Pauliomono/Kevin-the-Robot-Dog/CAD Files/servo motor/1.JPG

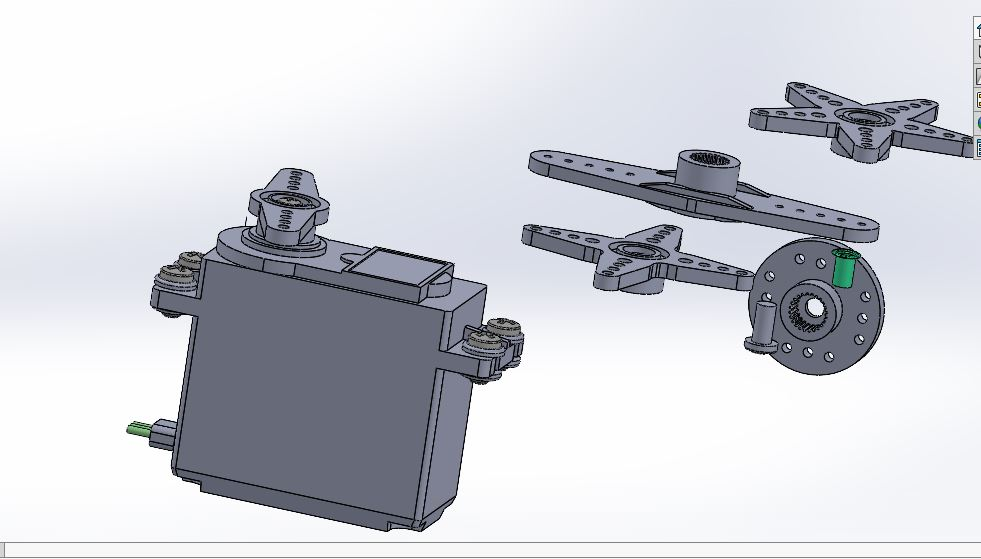
CAD Files/servo motor/1.JPG
