Pauliomono/Kevin-the-Robot-Dog/CAD Files/servo motor/2.JPG

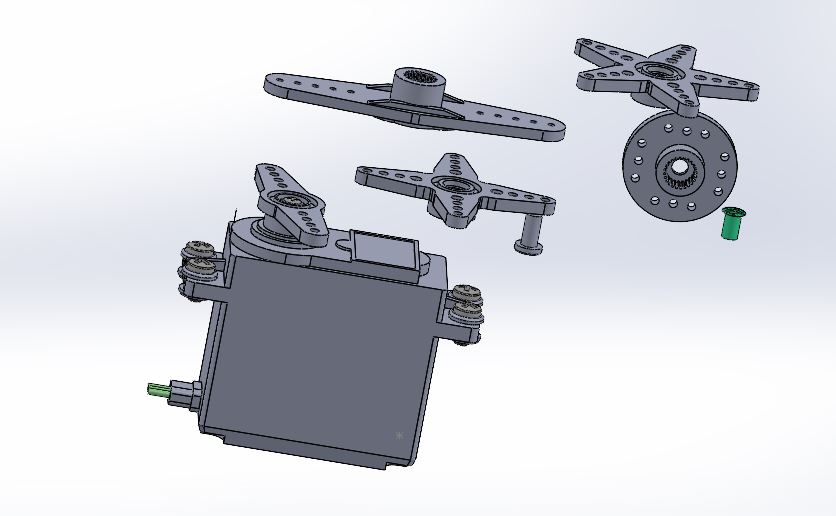
CAD Files/servo motor/2.JPG
