Pauliomono/Kevin-the-Robot-Dog/CAD Files/servo motor/3.JPG

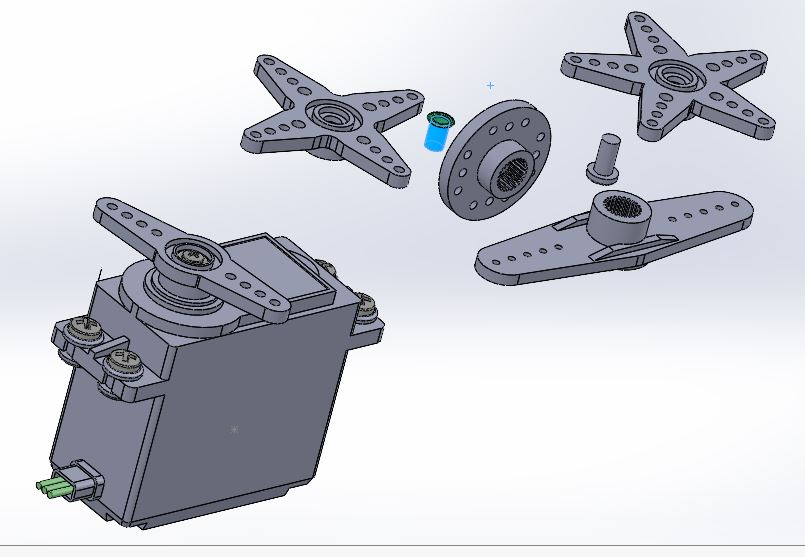
CAD Files/servo motor/3.JPG
