Pauliomono/Kevin-the-Robot-Dog/CAD Files/servo motor/4.JPG

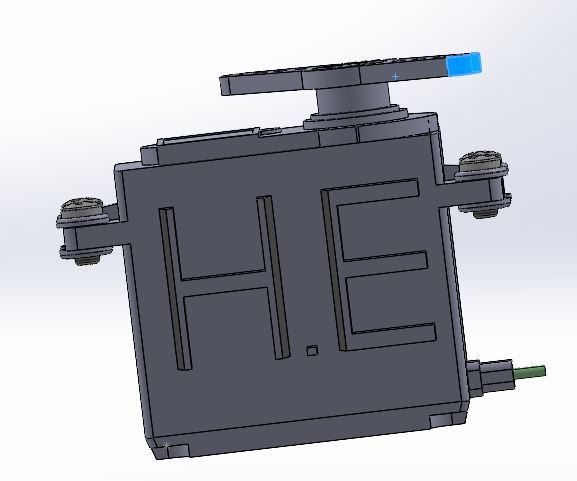
CAD Files/servo motor/4.JPG
