Pauliomono/Kevin-the-Robot-Dog/CAD Files/servo motor/part7.SLDPRT

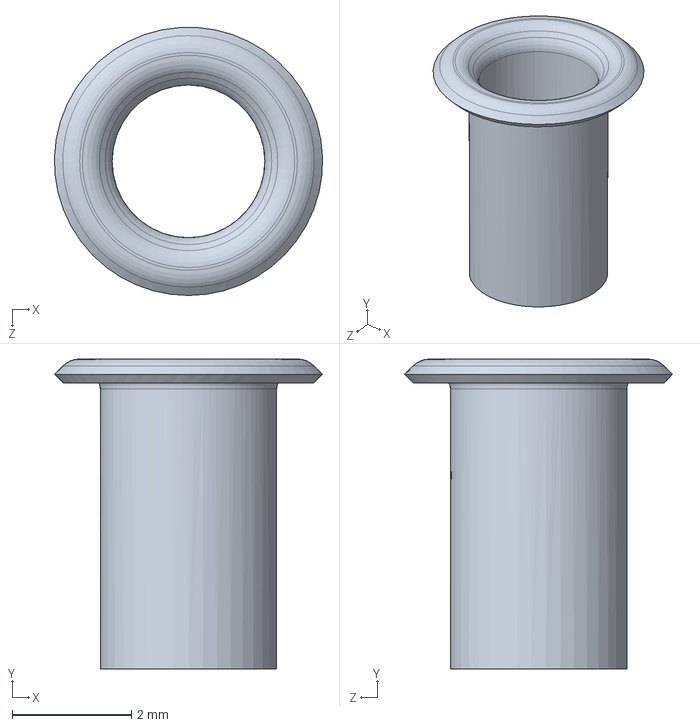
[picture p26: CAD file, 2022-06-29]
CAD Files/servo motor/part7.SLDPRT
4.50 x 5.20 x 4.49 mm
