Pauliomono/Kevin-the-Robot-Dog/CAD Files/servo motor/Parça2 - Kopya.SLDPRT

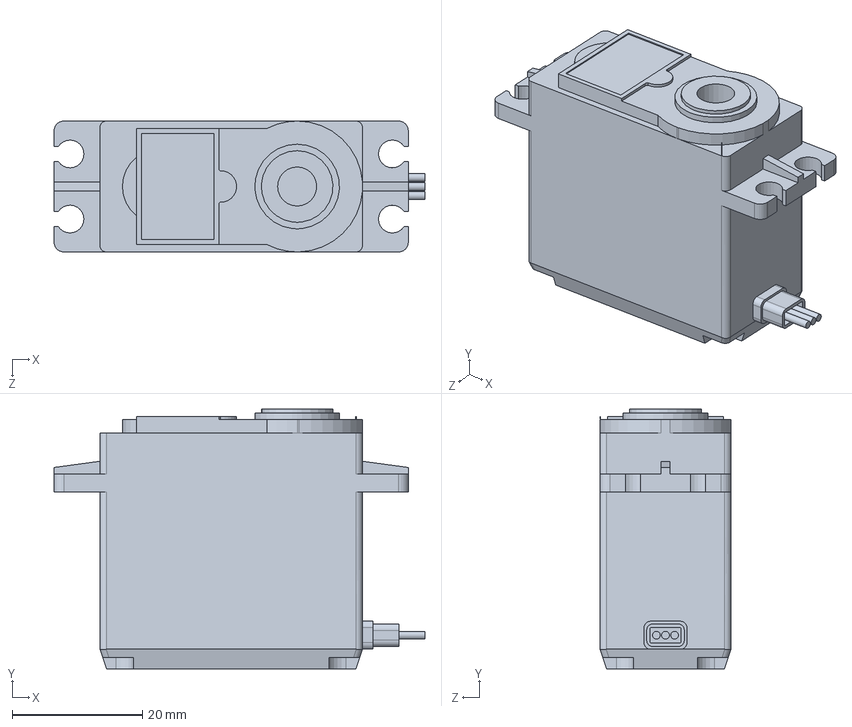
[picture p27: CAD file, 2022-06-29]
CAD Files/servo motor/Parça2 - Kopya.SLDPRT
57.0 x 39.8 x 20.1 mm
