Pauliomono/Kevin-the-Robot-Dog/CAD Files/servo-brackets-2.snapshot.3/U Long Bracket.SLDPRT

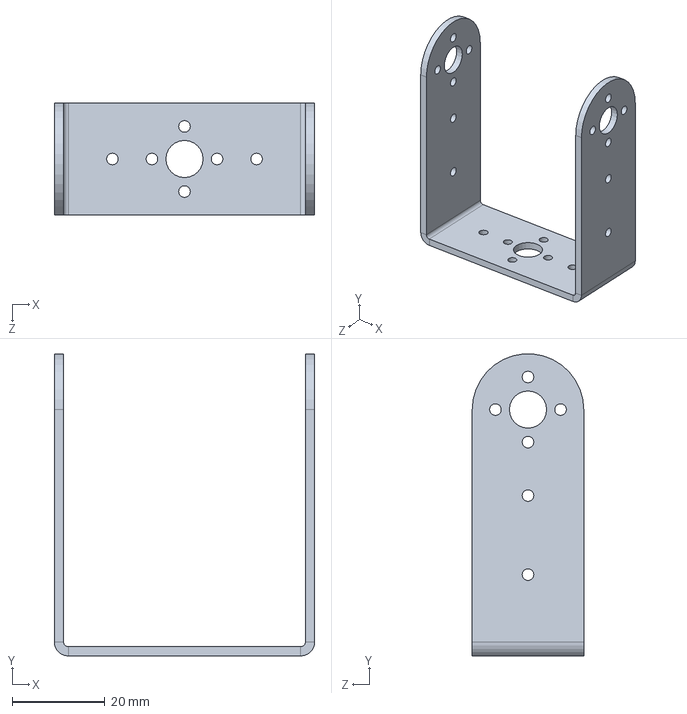
[picture p28: CAD file, 2022-06-29]
CAD Files/servo-brackets-2.snapshot.3/U Long Bracket.SLDPRT
56.0 x 64.9 x 24.0 mm
