Pauliomono/Kevin-the-Robot-Dog/CAD Files/PCB_guard.SLDPRT

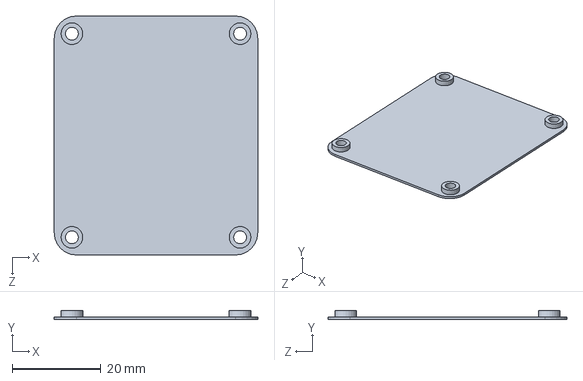
[picture p29: CAD file, 2022-06-29]
CAD Files/PCB_guard.SLDPRT
46.0 x 2.00 x 54.0 mm
