Pauliomono/Kevin-the-Robot-Dog/CAD Files/servo motor/Parça1.SLDPRT

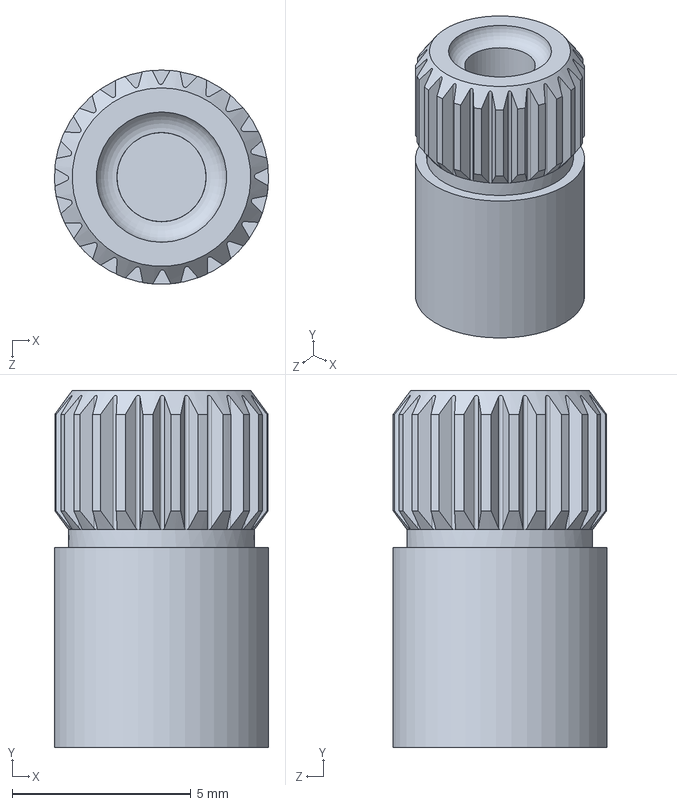
[picture p30: CAD file, 2022-06-29]
CAD Files/servo motor/Parça1.SLDPRT
6.00 x 10.0 x 5.99 mm
