Pauliomono/Kevin-the-Robot-Dog/CAD Files/servo-brackets-2.snapshot.3/Channel Bracket.SLDPRT

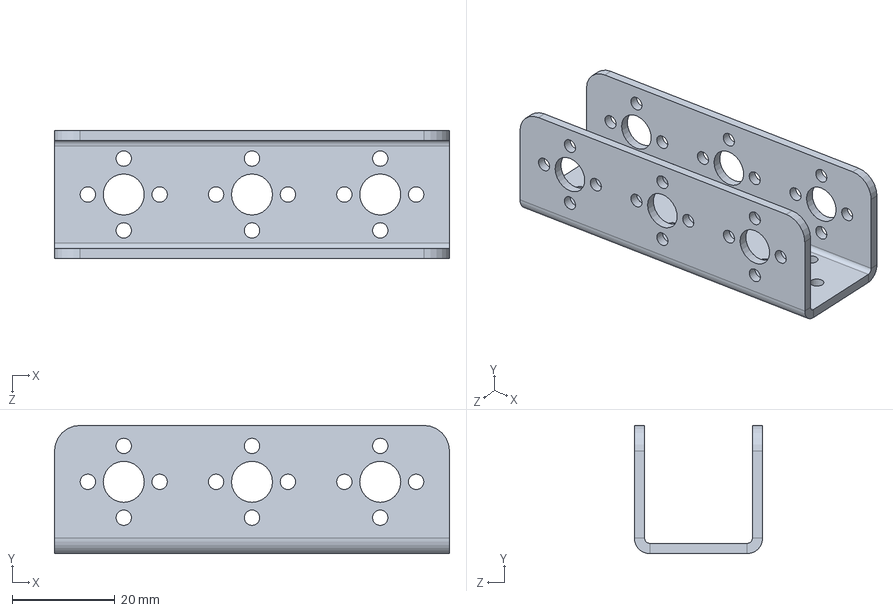
[picture p31: CAD file, 2022-06-29]
CAD Files/servo-brackets-2.snapshot.3/Channel Bracket.SLDPRT
77.0 x 25.0 x 25.0 mm
