Pauliomono/Kevin-the-Robot-Dog/CAD Files/servo motor/parça11,.SLDPRT

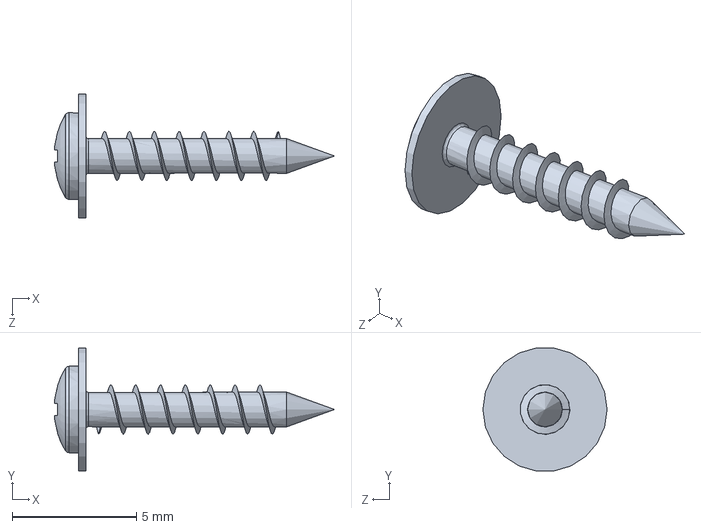
[picture p32: CAD file, 2022-06-29]
CAD Files/servo motor/parça11,.SLDPRT
11.3 x 4.95 x 5.00 mm
