Pauliomono/Kevin-the-Robot-Dog/CAD Files/servo-brackets-2.snapshot.3/Multi Purpose Bracket.SLDPRT

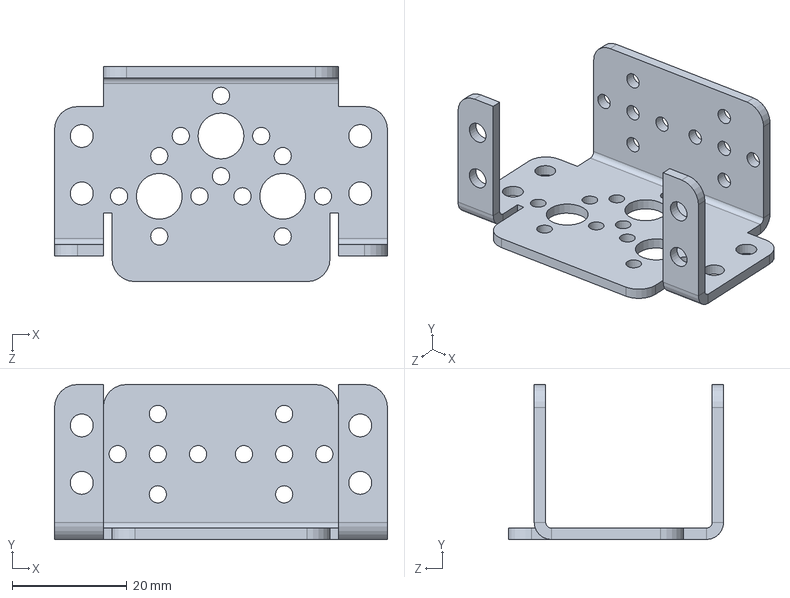
[picture p33: CAD file, 2022-06-29]
CAD Files/servo-brackets-2.snapshot.3/Multi Purpose Bracket.SLDPRT
58.0 x 27.0 x 37.5 mm
