Pauliomono/Kevin-the-Robot-Dog/CAD Files/servo motor/parça9.SLDPRT

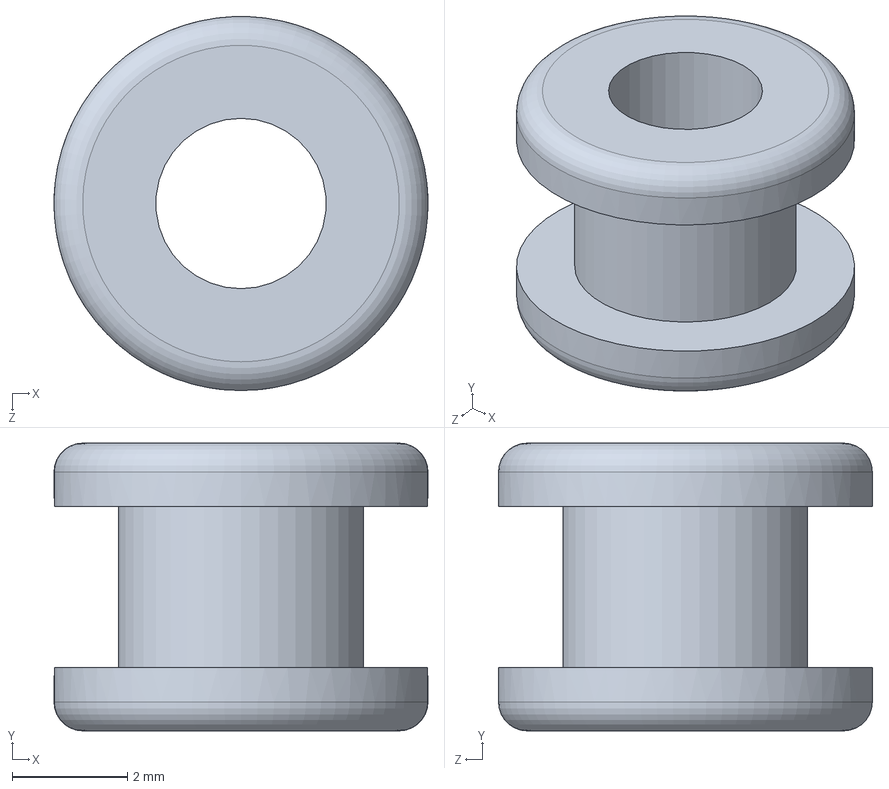
[picture p34: CAD file, 2022-06-29]
CAD Files/servo motor/parça9.SLDPRT
6.50 x 5.00 x 6.50 mm
