Pauliomono/Kevin-the-Robot-Dog/CAD Files/servo-brackets-2.snapshot.3/Offset Bracket.SLDPRT

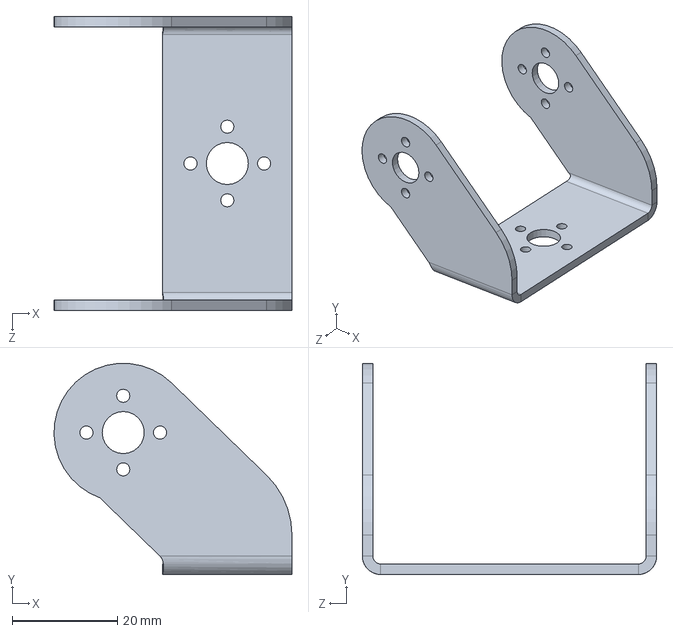
[picture p35: CAD file, 2022-06-29]
CAD Files/servo-brackets-2.snapshot.3/Offset Bracket.SLDPRT
45.3 x 40.1 x 56.0 mm
