Pauliomono/Kevin-the-Robot-Dog/CAD Files/hip_frame_2.SLDPRT

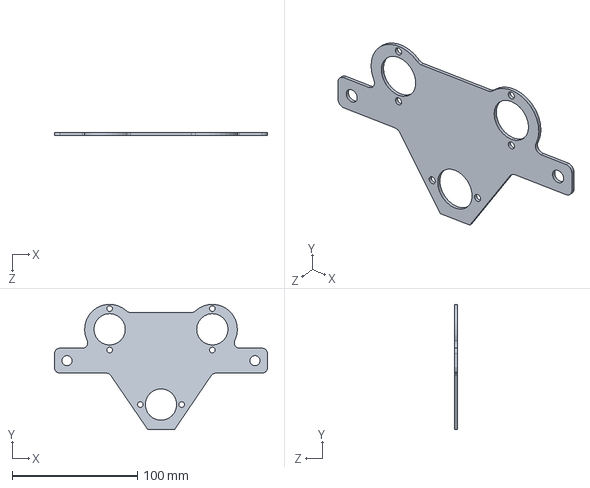
[picture p36: CAD file, 2022-06-29]
CAD Files/hip_frame_2.SLDPRT
170.0 x 99.9 x 2.00 mm
