Pauliomono/Kevin-the-Robot-Dog/CAD Files/servo motor/Parça6.SLDPRT

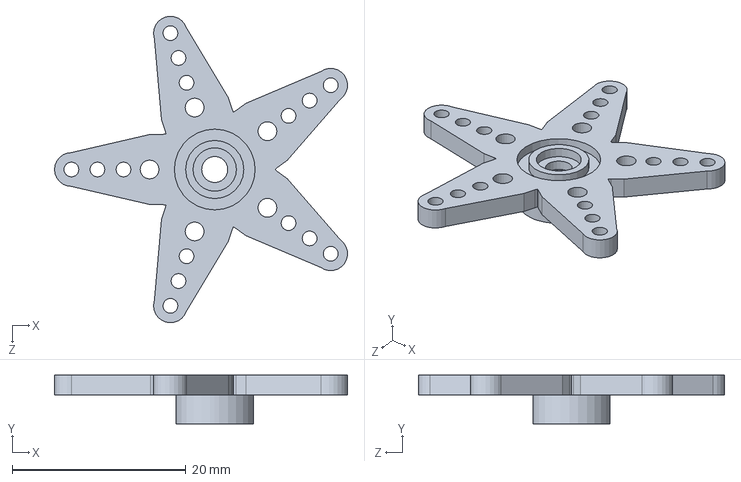
[picture p37: CAD file, 2022-06-29]
CAD Files/servo motor/Parça6.SLDPRT
33.7 x 5.60 x 35.3 mm
