Pauliomono/Kevin-the-Robot-Dog/CAD Files/servo motor/Parça2.SLDPRT

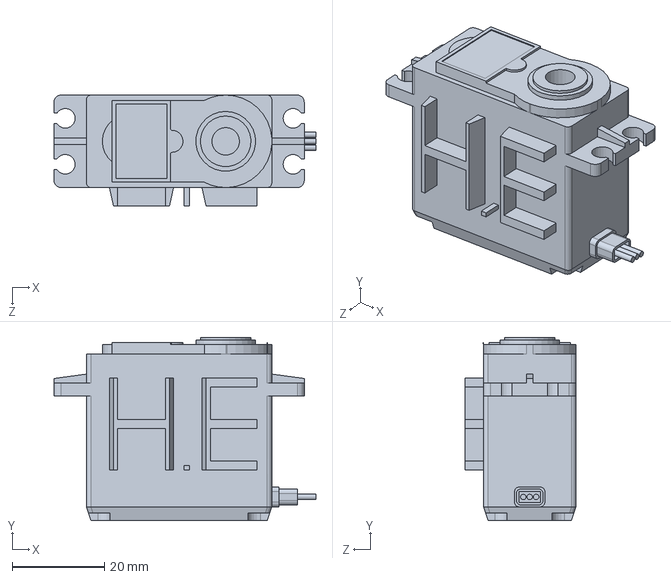
[picture p38: CAD file, 2022-06-29]
CAD Files/servo motor/Parça2.SLDPRT
57.0 x 39.8 x 24.1 mm
