Pauliomono/Kevin-the-Robot-Dog/CAD Files/frame_tube_1.SLDPRT

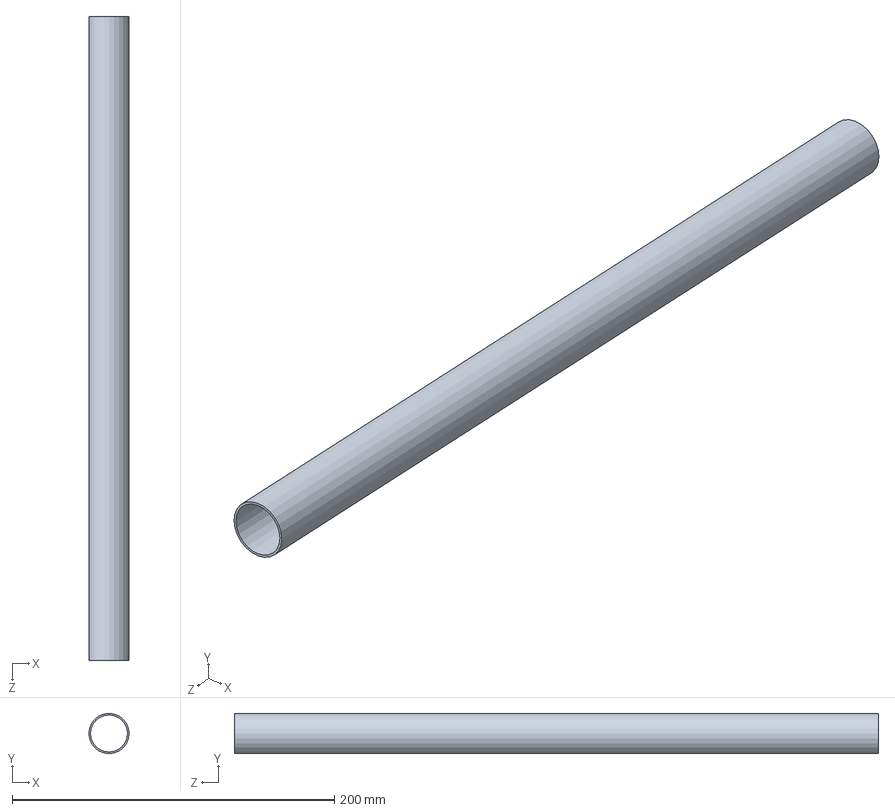
[picture p39: CAD file, 2022-06-29]
CAD Files/frame_tube_1.SLDPRT
25.0 x 25.0 x 400.0 mm
