Pauliomono/Kevin-the-Robot-Dog/CAD Files/servo motor/Parça5.SLDPRT

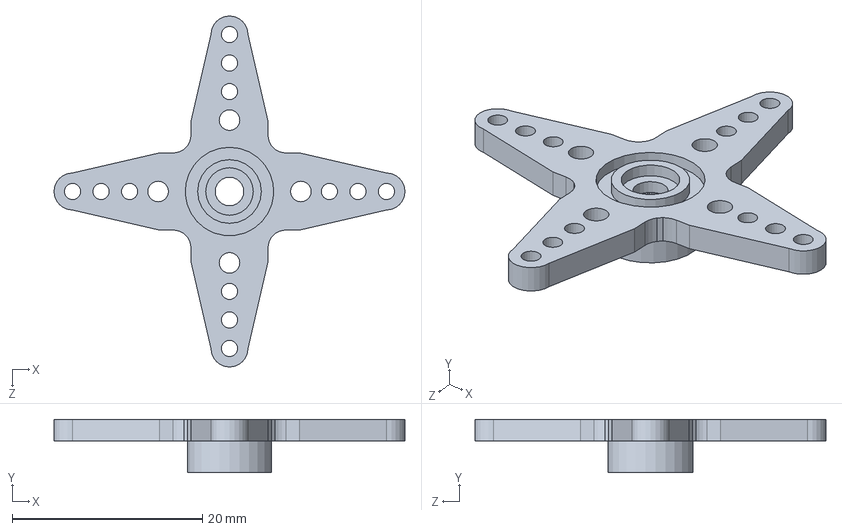
[picture p40: CAD file, 2022-06-29]
CAD Files/servo motor/Parça5.SLDPRT
36.9 x 5.60 x 36.9 mm
