Pauliomono/Kevin-the-Robot-Dog/CAD Files/leg_upper_1.SLDPRT

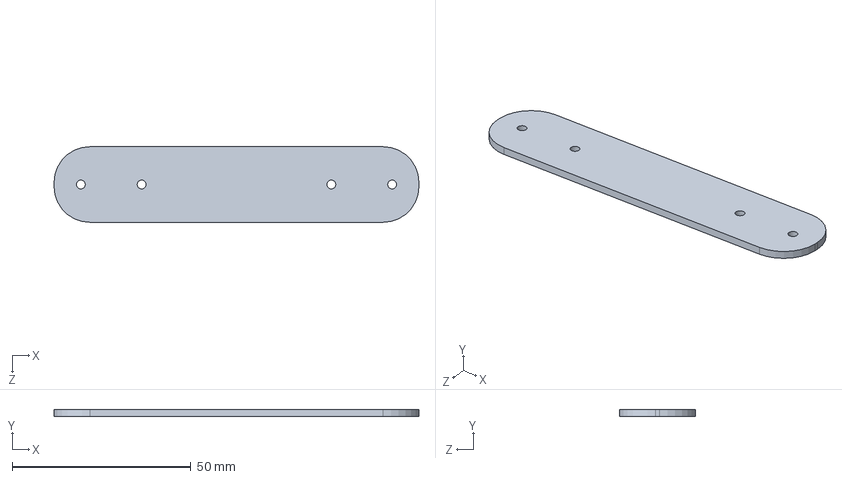
[picture p41: CAD file, 2022-06-29]
CAD Files/leg_upper_1.SLDPRT
102.0 x 2.00 x 21.1 mm
