Pauliomono/Kevin-the-Robot-Dog/CAD Files/servo motor/Parça3.SLDPRT

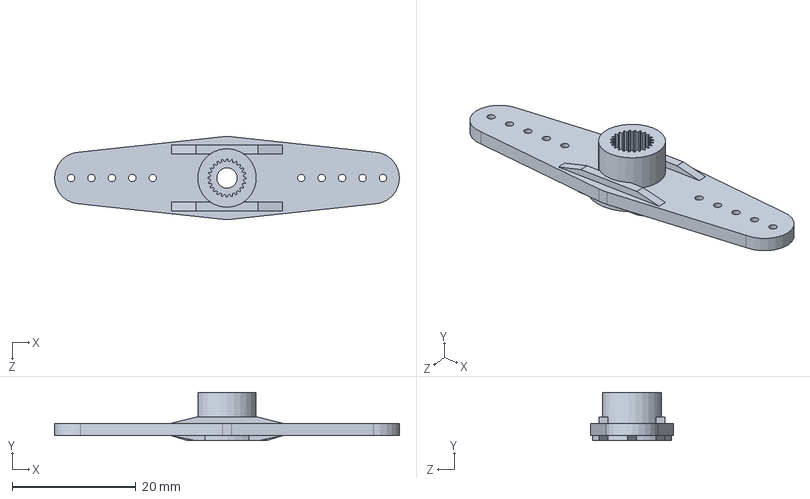
[picture p42: CAD file, 2022-06-29]
CAD Files/servo motor/Parça3.SLDPRT
55.7 x 7.80 x 13.3 mm
