Pauliomono/Kevin-the-Robot-Dog/CAD Files/servo motor/Parça8.SLDPRT

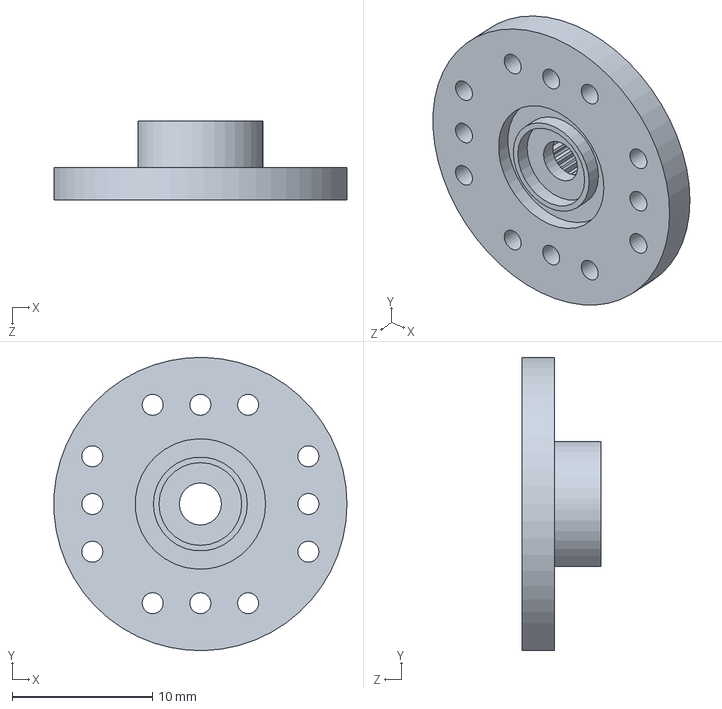
[picture p43: CAD file, 2022-06-29]
CAD Files/servo motor/Parça8.SLDPRT
20.9 x 20.9 x 5.60 mm
