Pauliomono/Kevin-the-Robot-Dog/CAD Files/hip_frame_1.SLDPRT

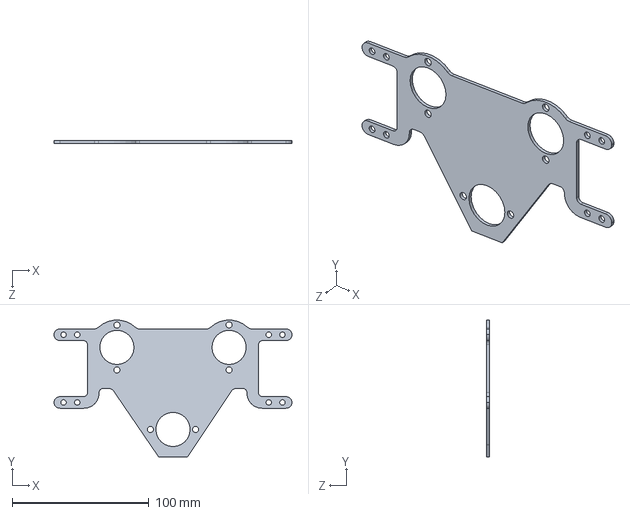
[picture p44: CAD file, 2022-06-29]
CAD Files/hip_frame_1.SLDPRT
174.0 x 99.9 x 2.00 mm
