Pauliomono/Kevin-the-Robot-Dog/CAD Files/servo motor/Parça10.SLDPRT

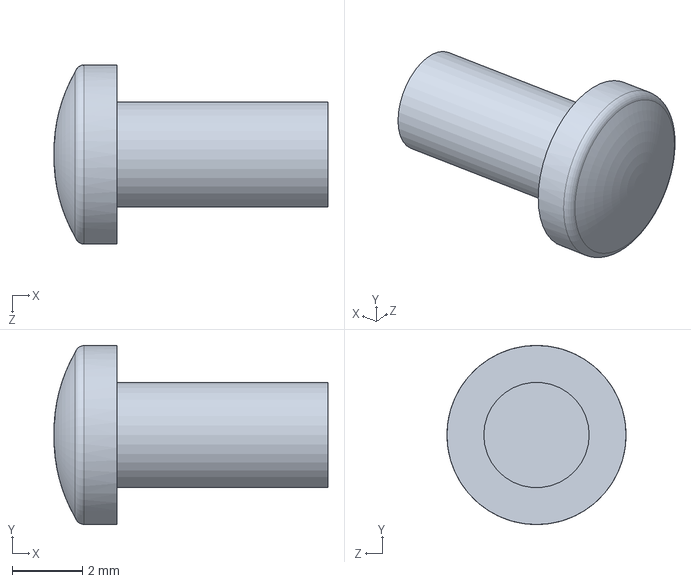
[picture p45: CAD file, 2022-06-29]
CAD Files/servo motor/Parça10.SLDPRT
7.80 x 5.10 x 5.10 mm
