Pauliomono/Kevin-the-Robot-Dog/CAD Files/tube_clamp_1.SLDPRT

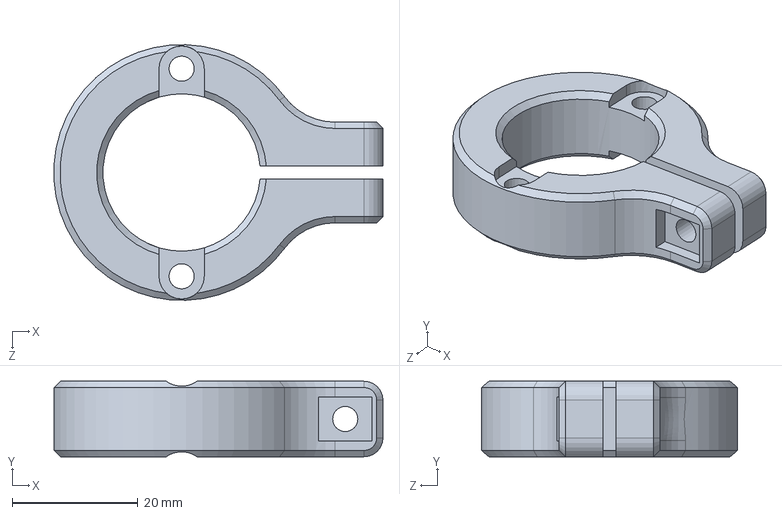
[picture p46: CAD file, 2022-06-29]
CAD Files/tube_clamp_1.SLDPRT
52.3 x 12.0 x 40.6 mm
