Pauliomono/Kevin-the-Robot-Dog/CAD Files/leg_lower_2.SLDPRT

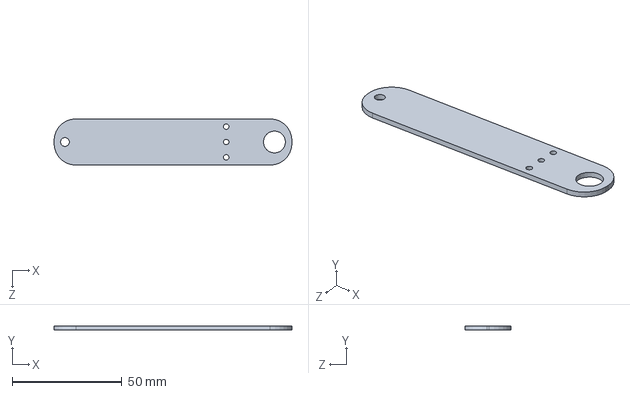
[picture p47: CAD file, 2022-06-29]
CAD Files/leg_lower_2.SLDPRT
108.5 x 2.00 x 21.1 mm
