Pauliomono/Kevin-the-Robot-Dog/CAD Files/hip_1.SLDPRT

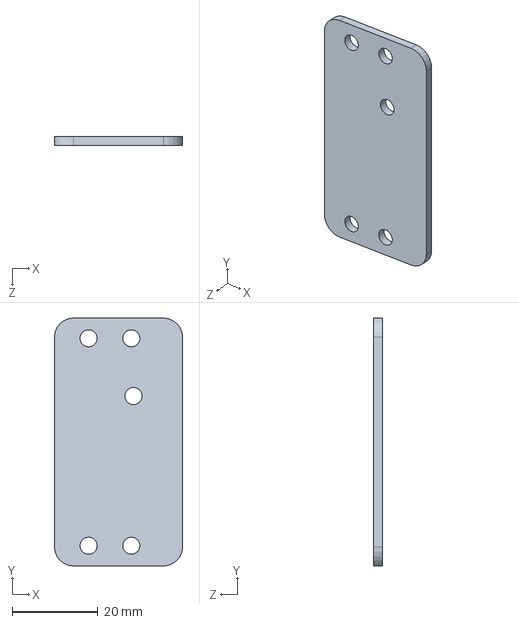
[picture p48: CAD file, 2022-06-29]
CAD Files/hip_1.SLDPRT
30.0 x 58.0 x 2.00 mm
