Pauliomono/Kevin-the-Robot-Dog/CAD Files/leg_lower_1.SLDPRT

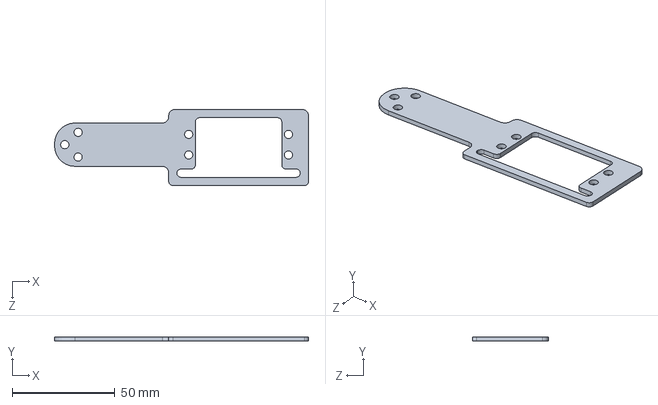
[picture p49: CAD file, 2022-06-29]
CAD Files/leg_lower_1.SLDPRT
123.5 x 2.00 x 37.0 mm
