Pauliomono/Kevin-the-Robot-Dog/Code/Kevin_v2.0.0/src/servos.h

#ifndef SERVOS_H
#define SERVOS_H

#include <Arduino.h>
#include <Servo.h>
#include <Adafruit_PWMServoDriver.h>
#include <configuration.h>
#include <balance_controller.h>

extern Servo hip1;
extern Servo shoulder1;
extern Servo knee1; 
extern Servo hip2;
extern Servo shoulder2;
extern Servo knee2; 
extern Servo hip3;
extern Servo shoulder3;
extern Servo knee3; 
extern Servo hip4;
extern Servo shoulder4;
extern Servo knee4;
extern Adafruit_PWMServoDriver pwm;

//leg angle structure
struct angles{
  float hip;
  float shoulder;
  float knee;
};

extern struct angles leg1;
extern struct angles leg2;
extern struct angles leg3;
extern struct angles leg4;

void write_servos();
int servodeadzone(int mils, int dead_center, int dead_width);
int deg2micros(float degrees);

#endif
