Pauliomono/Kevin-the-Robot-Dog/Code/Kevin_remote_v2.0.0/src/interpreter.h

#ifndef INTERPRET_INPUT2_H
#define INTERPRET_INPUT2H

#include <Arduino.h>

extern String datapacket;
extern int mode;

extern int xxx;
extern int yyy;
extern int packet;

extern int tune_mode;

void interpret_input_string();

#endif
