Pauliomono/Kevin-the-Robot-Dog/Code/Kevin_v2.0.0/src/debugging.cpp

#include <debugging.h>

void debug_timer(){

    Serial.print(debug_point);
    Serial.print("\t");
    Serial.println(micros() -debug_time);
    
    debug_time = micros();

    debug_point ++;

    if(debug_point > n_debug_points){
        debug_point = 1;
    }
}
